Scottapotamas/fuji-G-mount/electrical/scope-traces/P7-PWRON.png

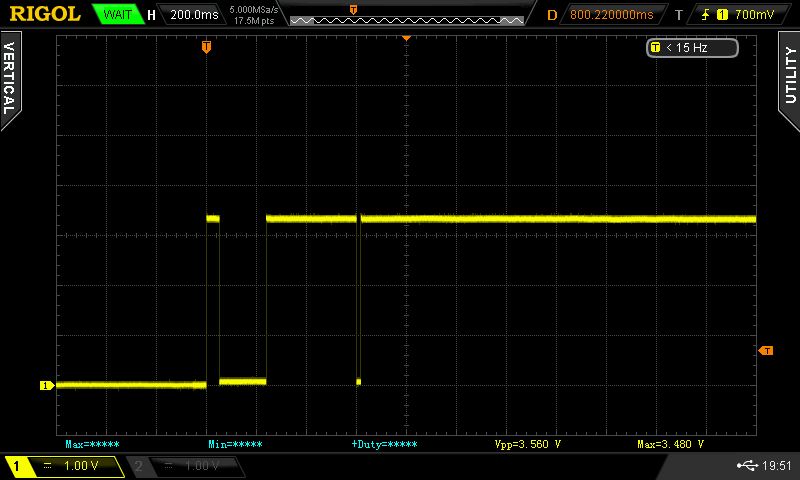
electrical/scope-traces/P7-PWRON.png
