Scottapotamas/fuji-G-mount/electrical/scope-traces/P8-FOCUS.png

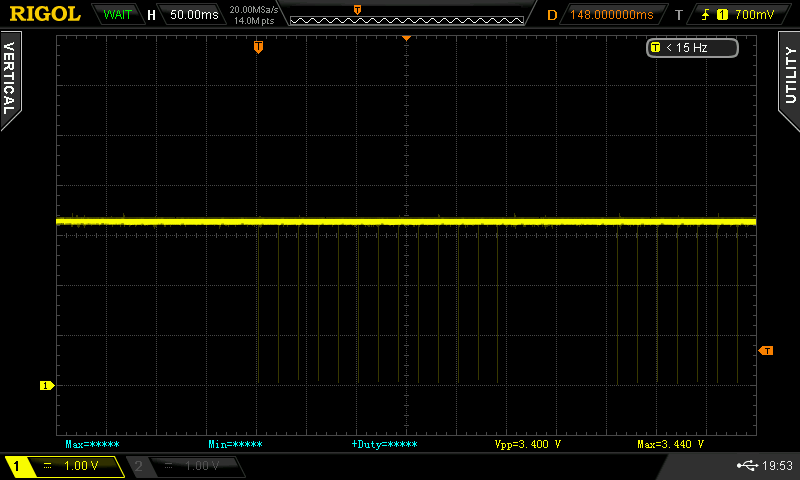
electrical/scope-traces/P8-FOCUS.png
