Scottapotamas/fuji-G-mount/electrical/scope-traces/P9-AFTER-FOCUS.png

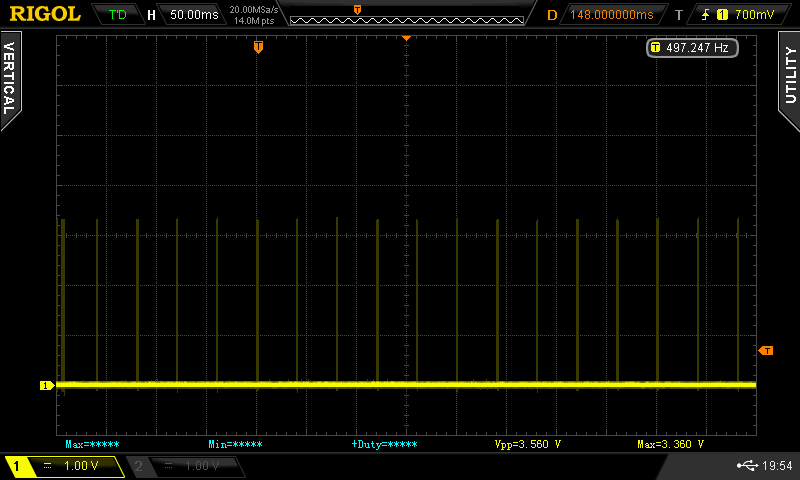
electrical/scope-traces/P9-AFTER-FOCUS.png
