Scottapotamas/fuji-G-mount/electrical/scope-traces/P11-FOCUS.png

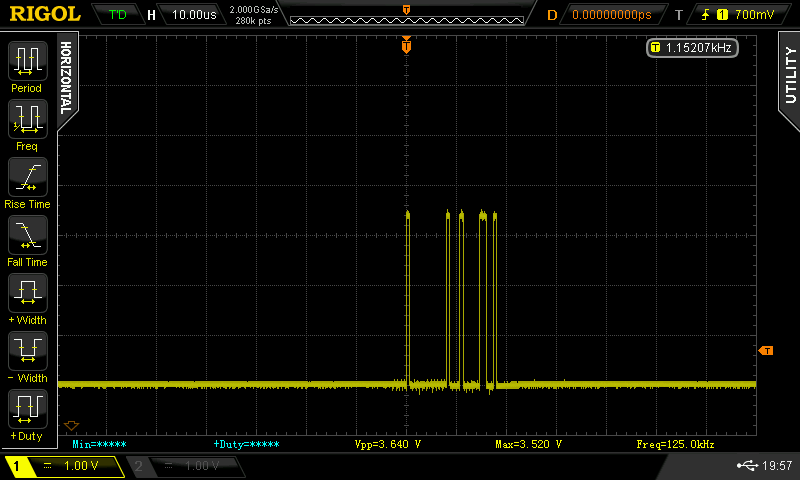
electrical/scope-traces/P11-FOCUS.png
