Scottapotamas/fuji-G-mount/electrical/springboard/output/renders/back.png

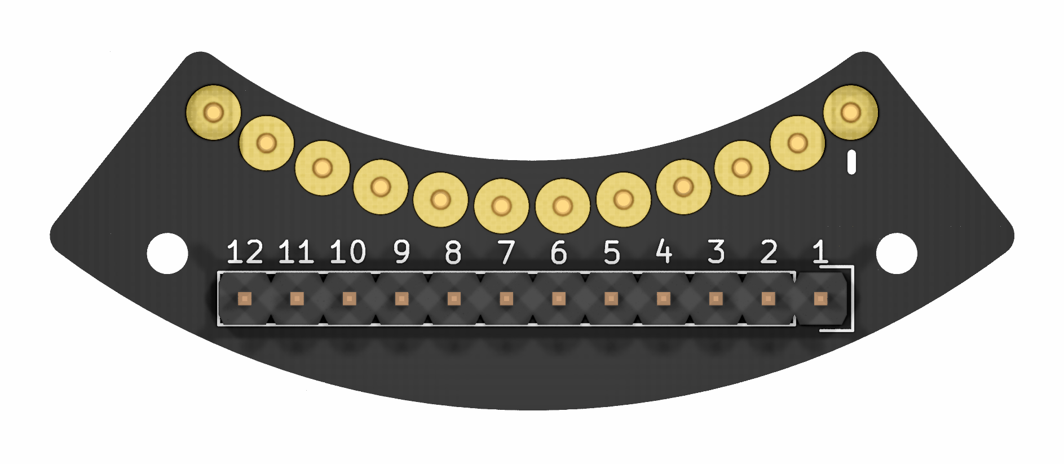
electrical/springboard/output/renders/back.png
