Scottapotamas/fuji-G-mount/electrical/springboard/output/renders/front.png

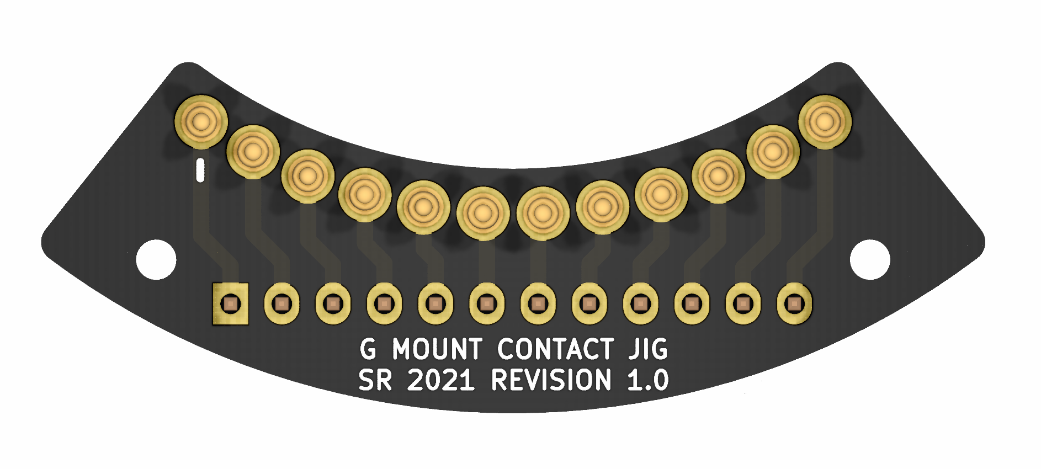
electrical/springboard/output/renders/front.png
