Scottapotamas/fuji-G-mount/mechanical/images/mcex-45g/DSCF4954.jpg

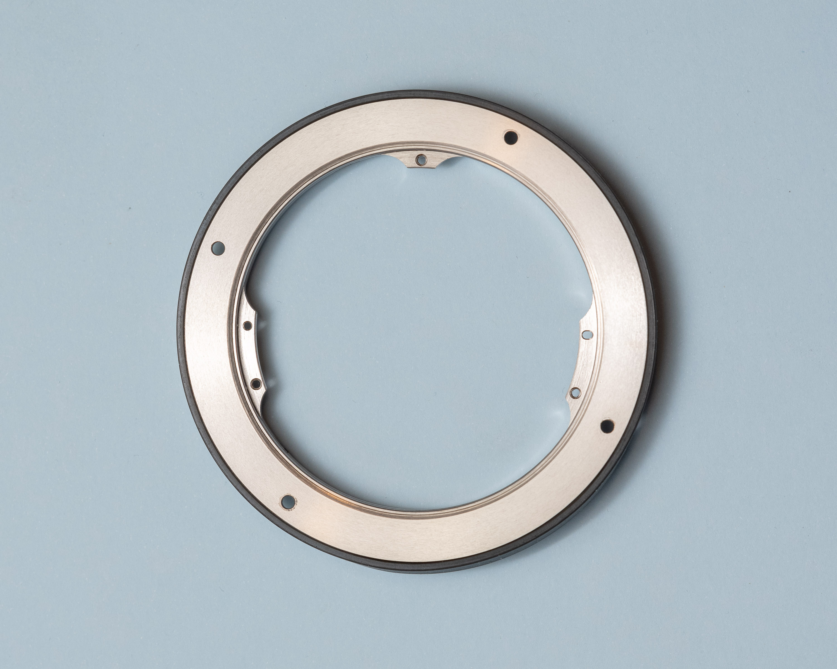
mechanical/images/mcex-45g/DSCF4954.jpg
