Scottapotamas/fuji-G-mount/mechanical/images/mcex-45g/DSCF4975.jpg

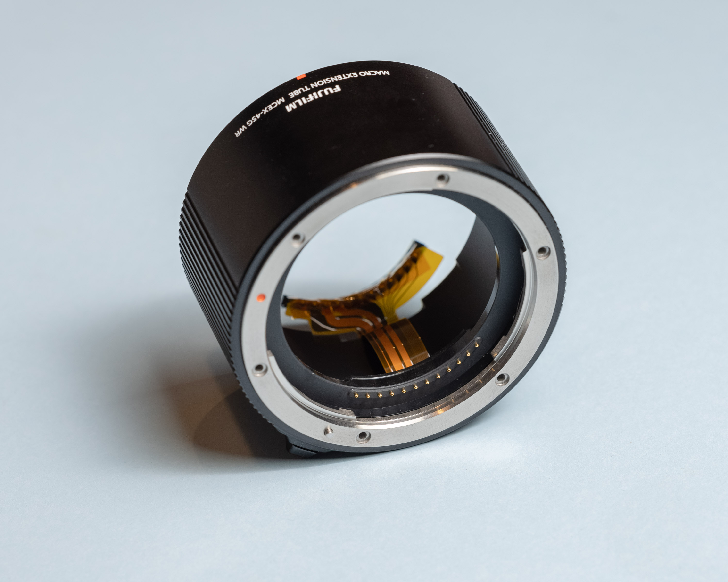
mechanical/images/mcex-45g/DSCF4975.jpg
