Scottapotamas/fuji-G-mount/mechanical/images/mcex-45g/DSCF4979.jpg

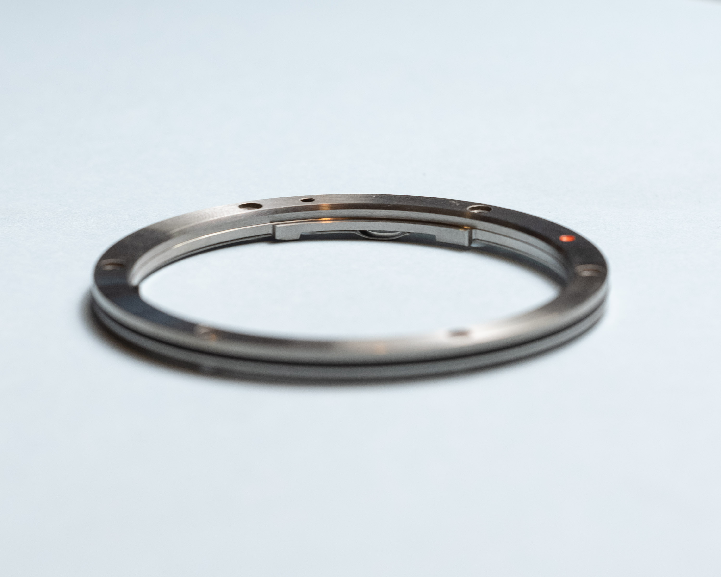
mechanical/images/mcex-45g/DSCF4979.jpg
