Scottapotamas/fuji-G-mount/mechanical/images/mcex-45g/DSCF4981.jpg

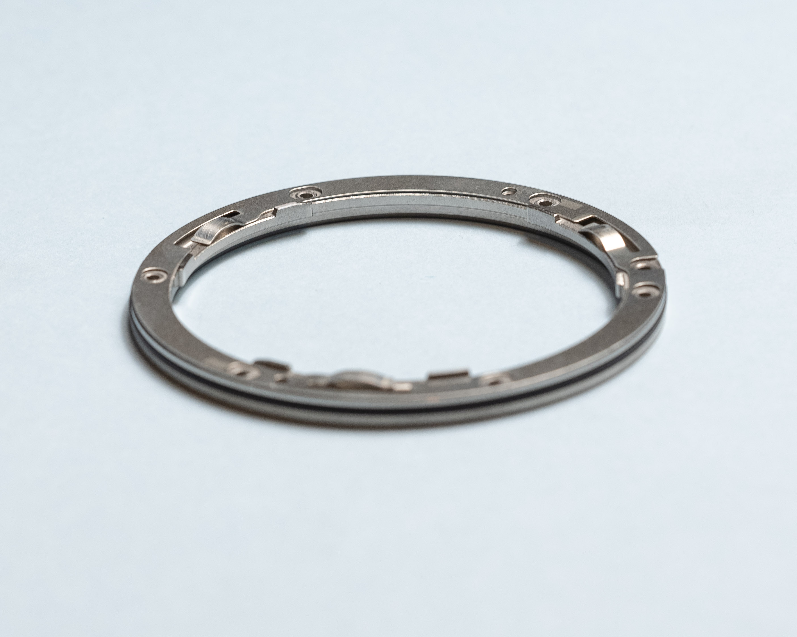
mechanical/images/mcex-45g/DSCF4981.jpg
