Scottapotamas/fuji-G-mount/mechanical/images/mcex-45g/DSCF5007.jpg

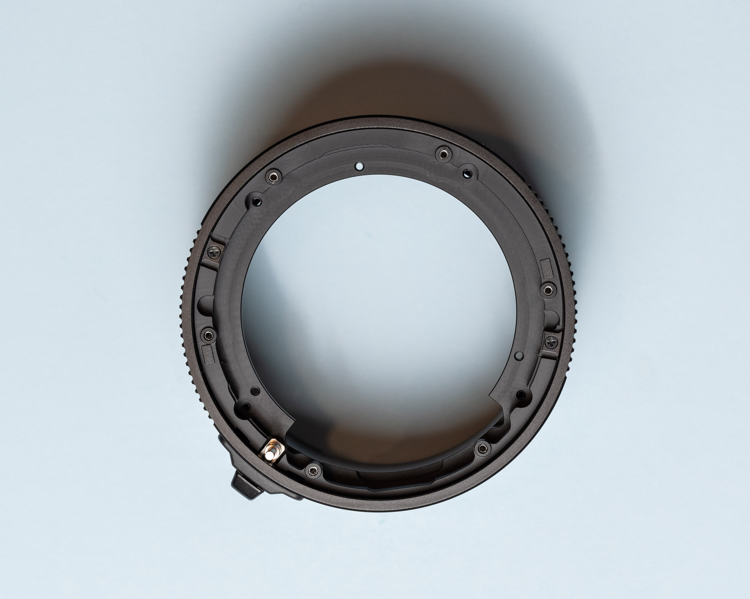
mechanical/images/mcex-45g/DSCF5007.jpg
