Scottapotamas/fuji-G-mount/protocol/images/110mm-focus-af-targeta-run1.png

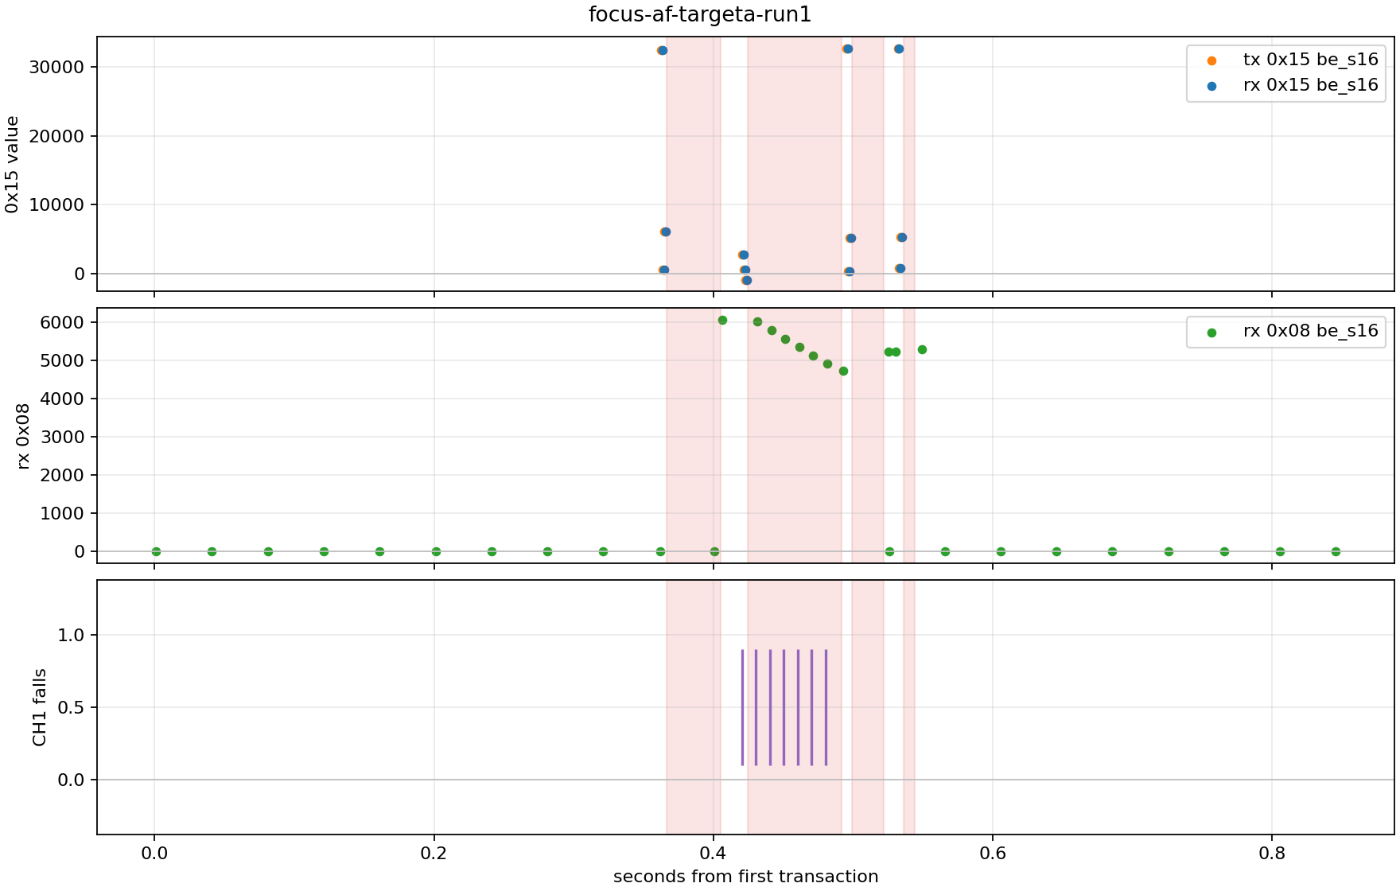
protocol/images/110mm-focus-af-targeta-run1.png
