Scottapotamas/fuji-G-mount/protocol/images/110mm-focus-ring-af-alternating.png

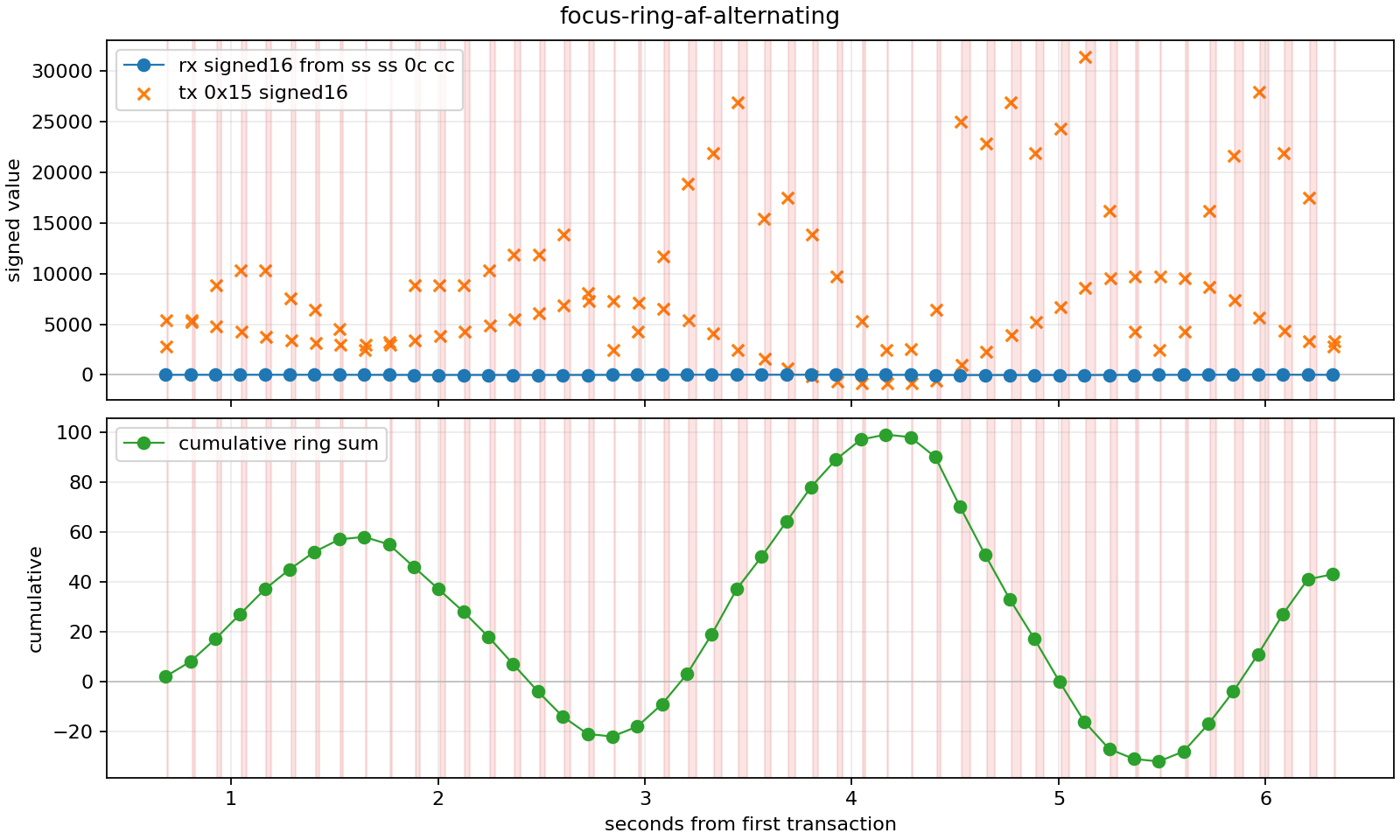
protocol/images/110mm-focus-ring-af-alternating.png
