Scottapotamas/fuji-G-mount/protocol/images/focus-ring-af-ccw-fast.png

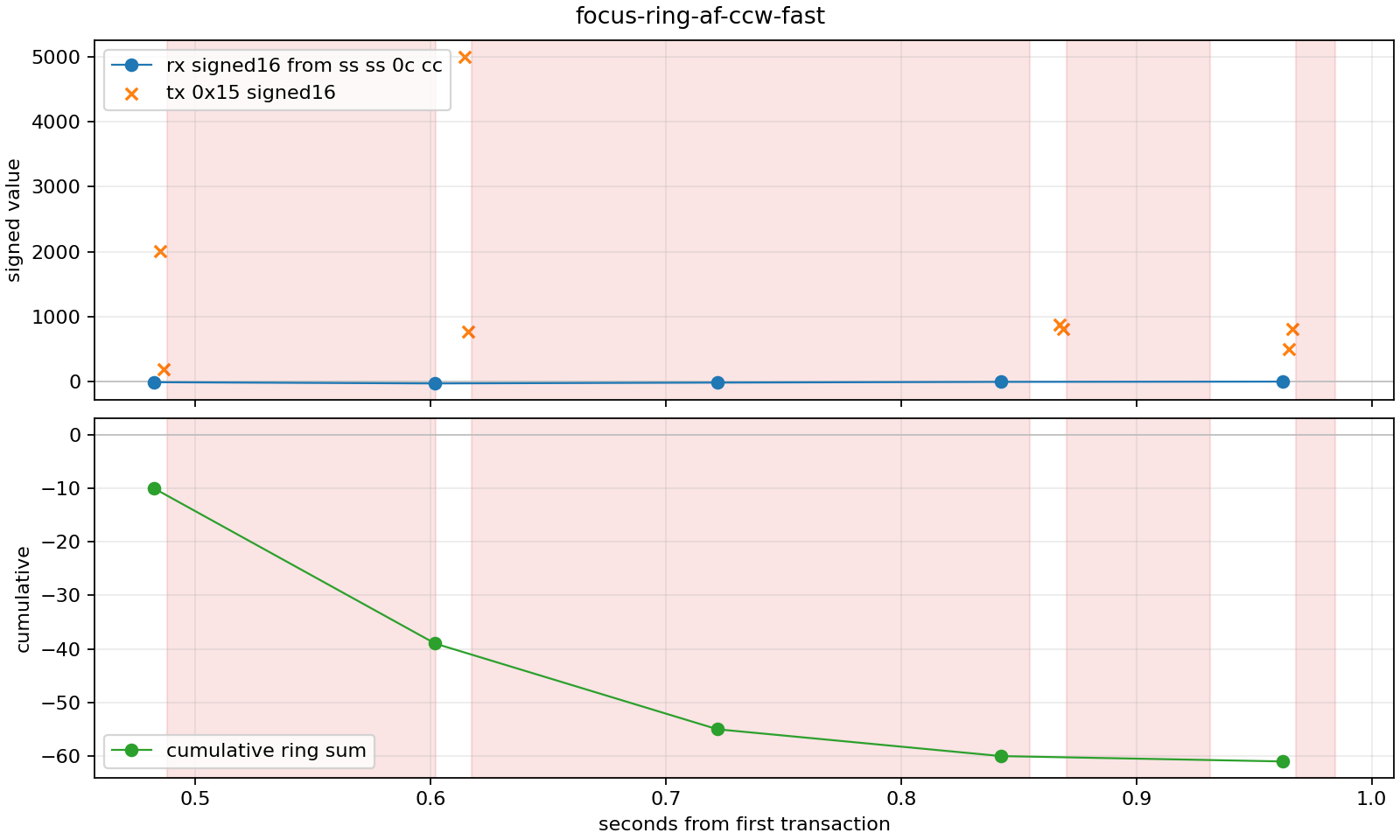
protocol/images/focus-ring-af-ccw-fast.png
