Scottapotamas/fuji-G-mount/protocol/images/focus-ring-cw-continuous-turns.png

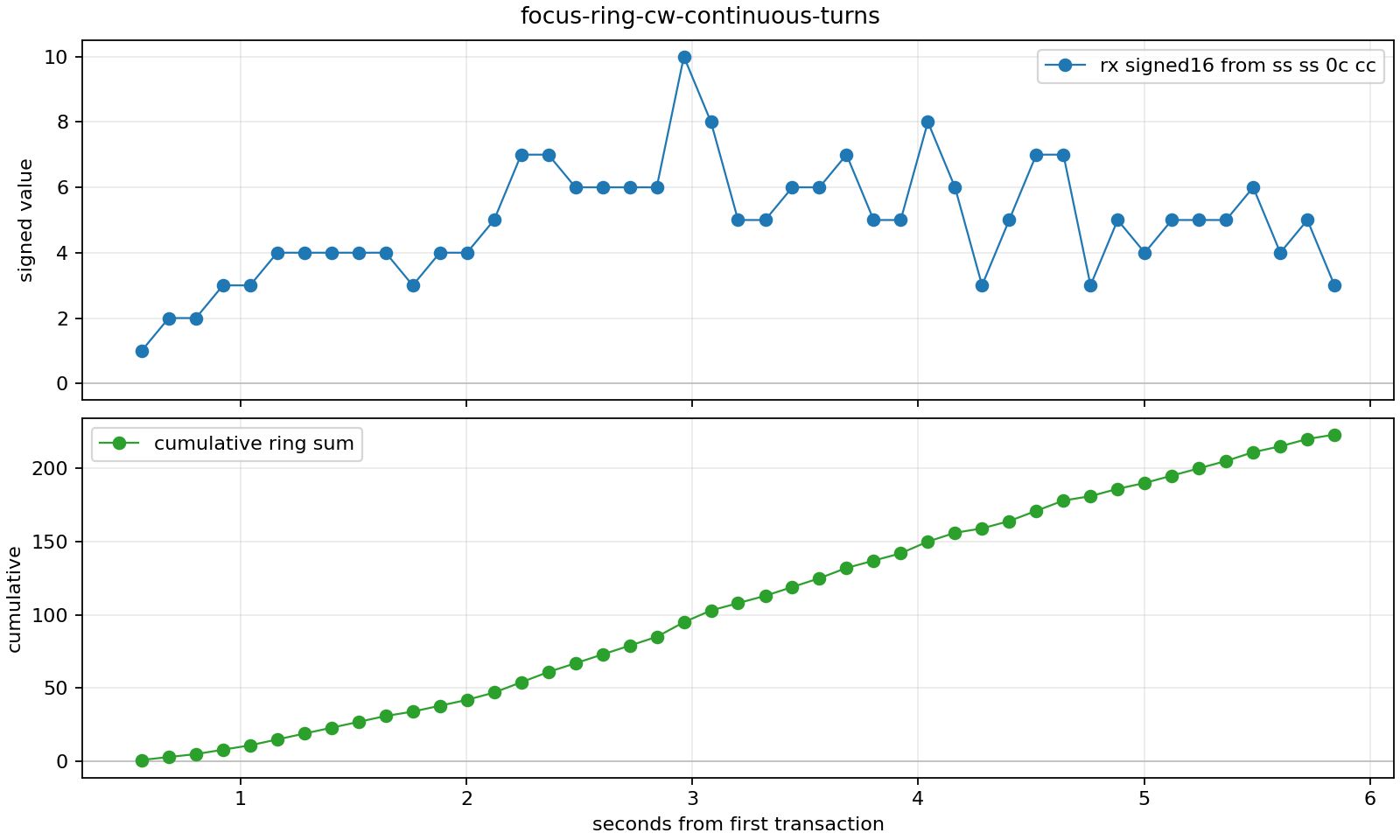
protocol/images/focus-ring-cw-continuous-turns.png
